someyob/Pico16cV2/pictures/PXL_20240703_185813182.jpg

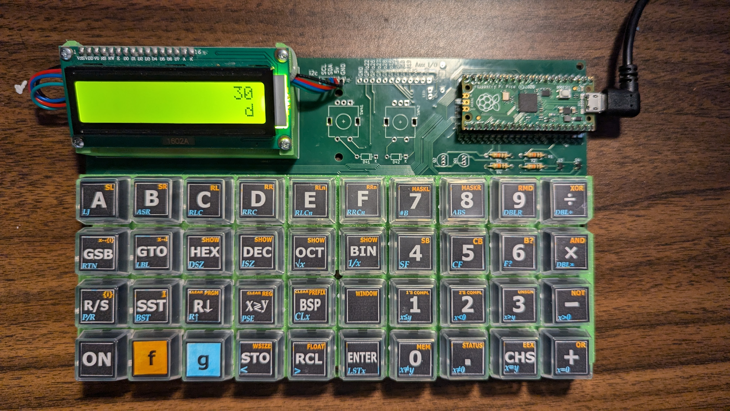
pictures/PXL_20240703_185813182.jpg
